Paschalis/Hardware-Login-Key/Images/gif/2.png

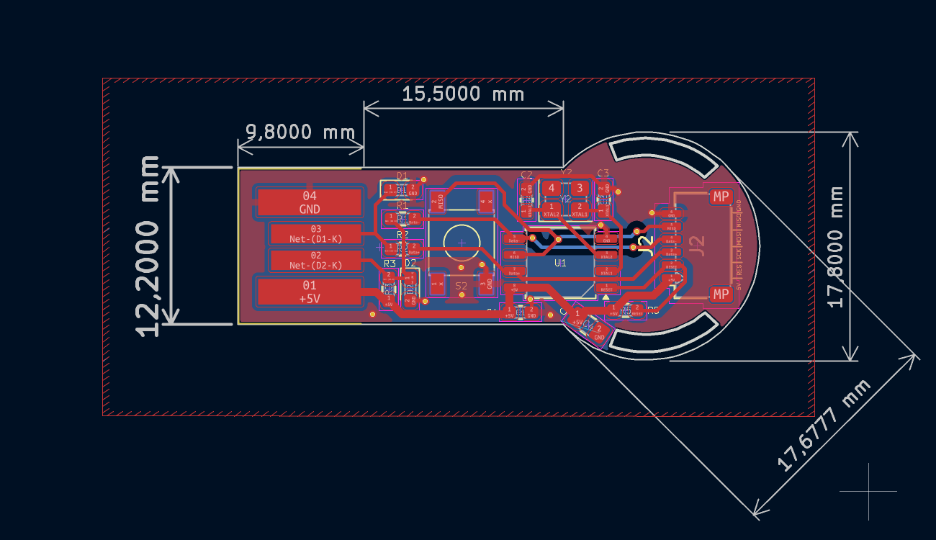
Images/gif/2.png
