Paschalis/Hardware-Login-Key/Images/QFN_Touch_TTP223_B.png

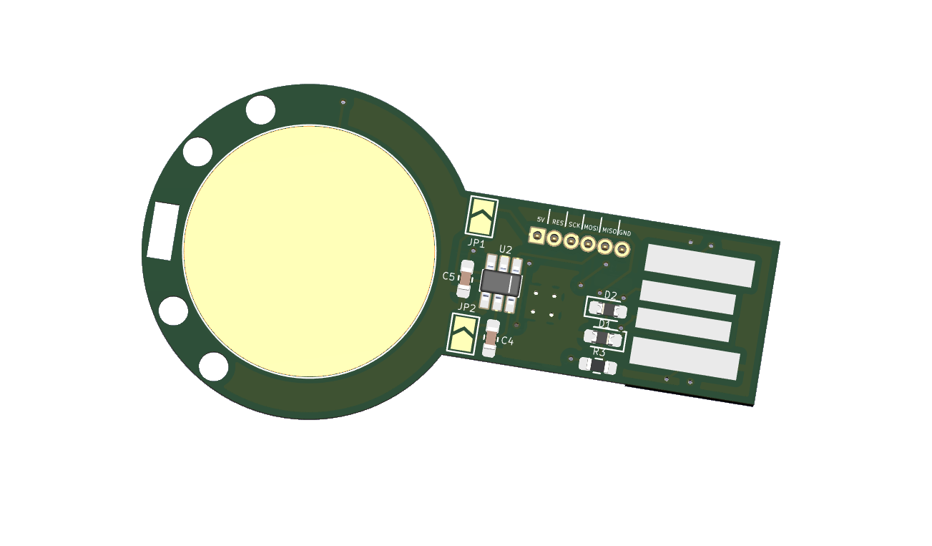
Images/QFN_Touch_TTP223_B.png
