Paschalis/Hardware-Login-Key/Images/QFN_Touch_TTP223_F.png

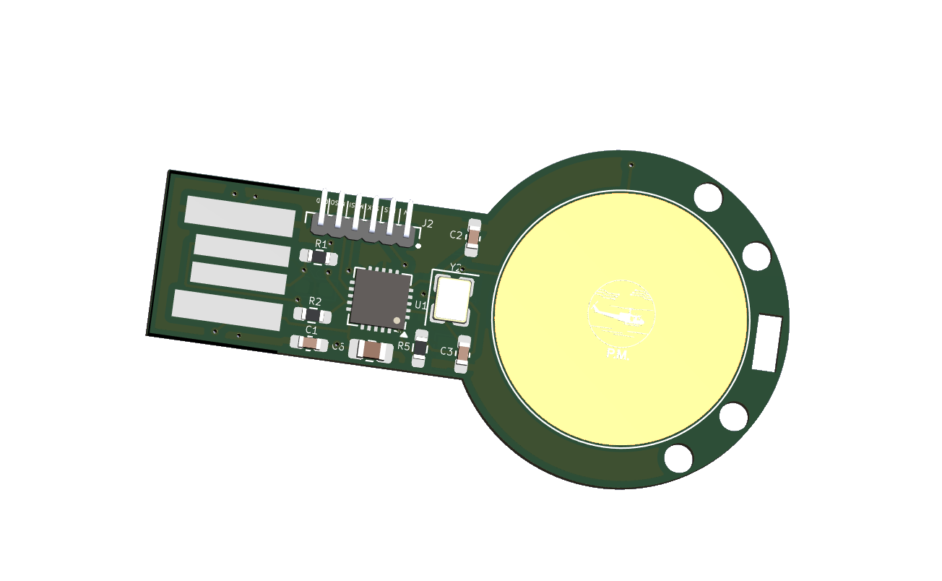
Images/QFN_Touch_TTP223_F.png
