Paschalis/Hardware-Login-Key/ATtiny85_Simple_Code_Test/C_Version/notes.h

#ifndef NOTES_H
#define NOTES_H

// --- Note Frequency Definitions (in Hz) ---
// This header maps musical notes to their standard frequencies.
// A rest is defined as 0 Hz.

#define NOTE_REST 0

// Octave 4
#define NOTE_C4  262
#define NOTE_CS4 277
#define NOTE_D4  294
#define NOTE_DS4 311
#define NOTE_E4  330
#define NOTE_F4  349
#define NOTE_FS4 370
#define NOTE_G4  392
#define NOTE_GS4 415
#define NOTE_A4  440
#define NOTE_AS4 466
#define NOTE_B4  494

// Octave 5
#define NOTE_C5  523
#define NOTE_D5  587
#define NOTE_E5  659
#define NOTE_F5  698
#define NOTE_G5  784
#define NOTE_A5  880
#define NOTE_B5  988

#endif // NOTES_H
